BoujeeEnjinia1701/bankhaul/cad/drawings/BKH-DWG-101.pdf

### BUILD PLAN SKETCH, PLAN NOT YET BUILT BankHaul · github.com/BoujeeEnjinia1701/bankhaul

FRONT VIEW
Scale 1:20; looking at the front (along +Y)

TOP VIEW
Scale 1:20; looking down (along -Z)

RIGHT VIEW
Scale 1:20; looking at the right side (along -X)

350

500 1408

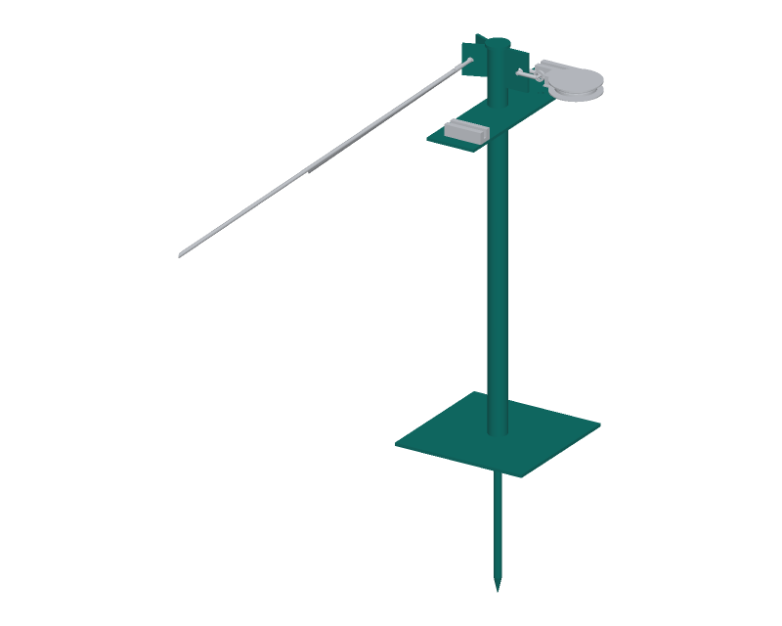
[picture p33: figure]

WHERE IT GOES
This part in colour, its neighbours in grey

HOW TO MAKE IT AND HOW IT FITS
Tube 992 long, ends square; foot plate 350 x 350 x 8 welded under it Spike 20 round, 400 below the plate centre, ground to a point
Cap disc 60 dia x 8 welded on the top of the tube
Pad eye 8 plate: 18 hole 64 from the post axis, 950 up, facing the water Two stay lugs 8 plate: 15 holes 960 up, 22 deg either side of straight back Cleat bar 130 x 500 x 8: 48.9 hole, slip on, top 850 up, weld all round Cleat bar holes: four 9 at 170 and 230 either side; one 15 tie-off hole Square the tube to the foot plate within 1 deg; weld all round
Check: pad eye hole and lug holes take a 10 mm shackle pin freely
REV | DESCRIPTION | DATE | BY
P1 | Making sketch for the prototype build plan | 2026-10-03 | AC
BANKHAUL | github.com/BoujeeEnjinia1701/bankhaul

## Bank post weldment: making sketch

DRAWING NO.
BKH-DWG-101

REV
P1

SHEET
1 of 1

SIZE

## ANSI B

SCALE
1:20

UNITS
mm
PROJECTION | DATE
2026-10-03

DRAWN
Amish Chadha

MATERIAL / NOTES
48.3 x 3.2 tube; 8 mm plate; 20 mm round bar; zinc-rich paint
Licensed CERN-OHL-S-2.0 · Design Molecule Lab · designmolecule.com | Generated from cad/src; do not edit by hand
