BoujeeEnjinia1701/bankhaul/cad/drawings/BKH-DWG-106.pdf

### BUILD PLAN SKETCH, PLAN NOT YET BUILT BankHaul · github.com/BoujeeEnjinia1701/bankhaul

FRONT VIEW
Scale 1:5; looking at the front (along +Y)

TOP VIEW
Scale 1:5; looking down (along -Z)

RIGHT VIEW
Scale 1:5; looking at the right side (along -X)

657

16 92

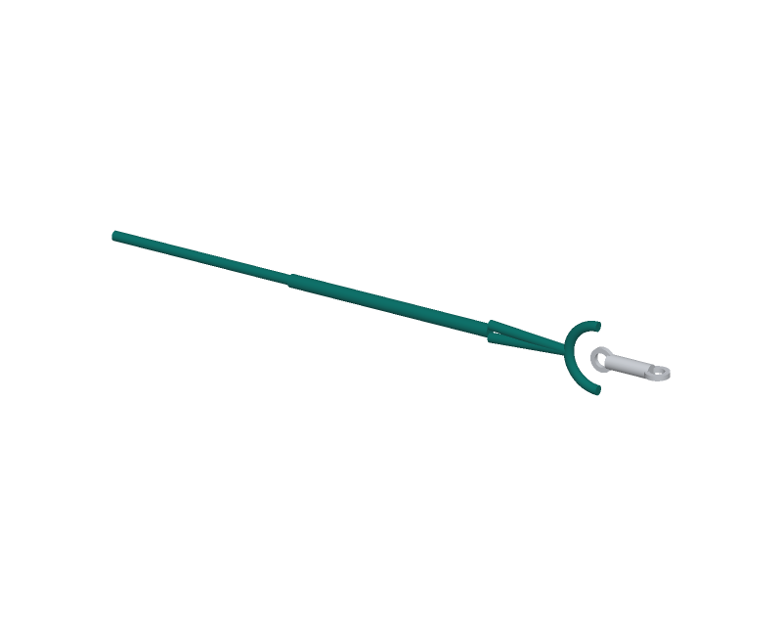
[picture p34: figure]

WHERE IT GOES
This part in colour, its neighbours in grey

HOW TO MAKE IT AND HOW IT FITS
Cut two halves of 55 m from the 120 m coil; tape and melt the ends Splice a soft eye 80 long round one swivel eye in each half; five tucks Lead each plain end round the other ring: round turn and two half hitches Set the length so the rings lie at the blocks when the loop is snug
Seize the knot's tail and coil any surplus at the ring, never between rings Check: each ring turns freely on its swivel under a hand pull
REV | DESCRIPTION | DATE | BY
P1 | Making sketch for the prototype build plan | 2026-10-03 | AC
BANKHAUL | github.com/BoujeeEnjinia1701/bankhaul

## Rope loop half and swivel ring: making sketch

DRAWING NO.
BKH-DWG-106

REV
P1

SHEET
1 of 1

SIZE

## ANSI B

SCALE
1:5

UNITS
mm
PROJECTION | DATE
2026-10-03

DRAWN
Amish Chadha

MATERIAL / NOTES
12 mm floating polysteel rope; eye-to-eye swivel
Licensed CERN-OHL-S-2.0 · Design Molecule Lab · designmolecule.com | Generated from cad/src; do not edit by hand
