BoujeeEnjinia1701/bankhaul/cad/drawings/BKH-DWG-107.pdf

### BUILD PLAN SKETCH, PLAN NOT YET BUILT BankHaul · github.com/BoujeeEnjinia1701/bankhaul

FRONT VIEW
Scale 1:20; looking at the front (along +Y)

TOP VIEW
Scale 1:20; looking down (along -Z)

RIGHT VIEW
Scale 1:20; looking at the right side (along -X)

83

8 1525

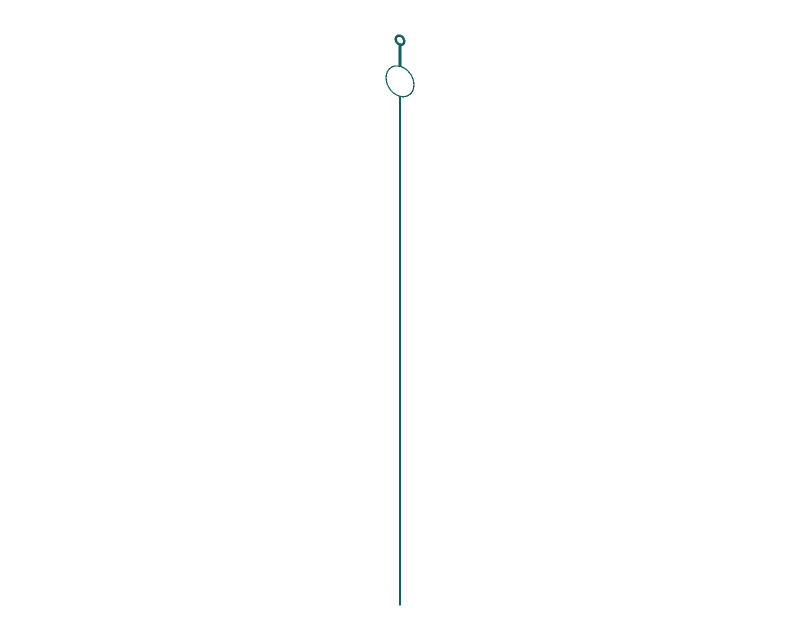
[picture p35: figure]

WHERE IT GOES
This part in colour, its neighbours in grey

HOW TO MAKE IT AND HOW IT FITS
Bridle 1,500 of 6 mm cord; bowline to the net's head and foot ropes
Weak link: one loop of the chosen cord, 80 long, joining hook and bridle Choose the cord by pulling three samples: each must release at 500 to 700 N Snap hook clips to a swivel ring (far end) or the tie-off hole (near end)
Make two; mark the weak link cord with paint so it is never swapped
Check: the hook opens with one hand and snaps shut by itself
REV | DESCRIPTION | DATE | BY
P1 | Making sketch for the prototype build plan | 2026-10-03 | AC
BANKHAUL | github.com/BoujeeEnjinia1701/bankhaul

## Net bridle with weak link: making sketch

DRAWING NO.
BKH-DWG-107

REV
P1

SHEET
1 of 1

SIZE

## ANSI B

SCALE
1:20

UNITS
mm
PROJECTION | DATE
2026-10-03

DRAWN
Amish Chadha

MATERIAL / NOTES
6 mm polyester cord; braided weak link cord; 60 mm stainless snap hook
Licensed CERN-OHL-S-2.0 · Design Molecule Lab · designmolecule.com | Generated from cad/src; do not edit by hand
