BoujeeEnjinia1701/bankhaul/cad/drawings/BKH-DWG-001.png

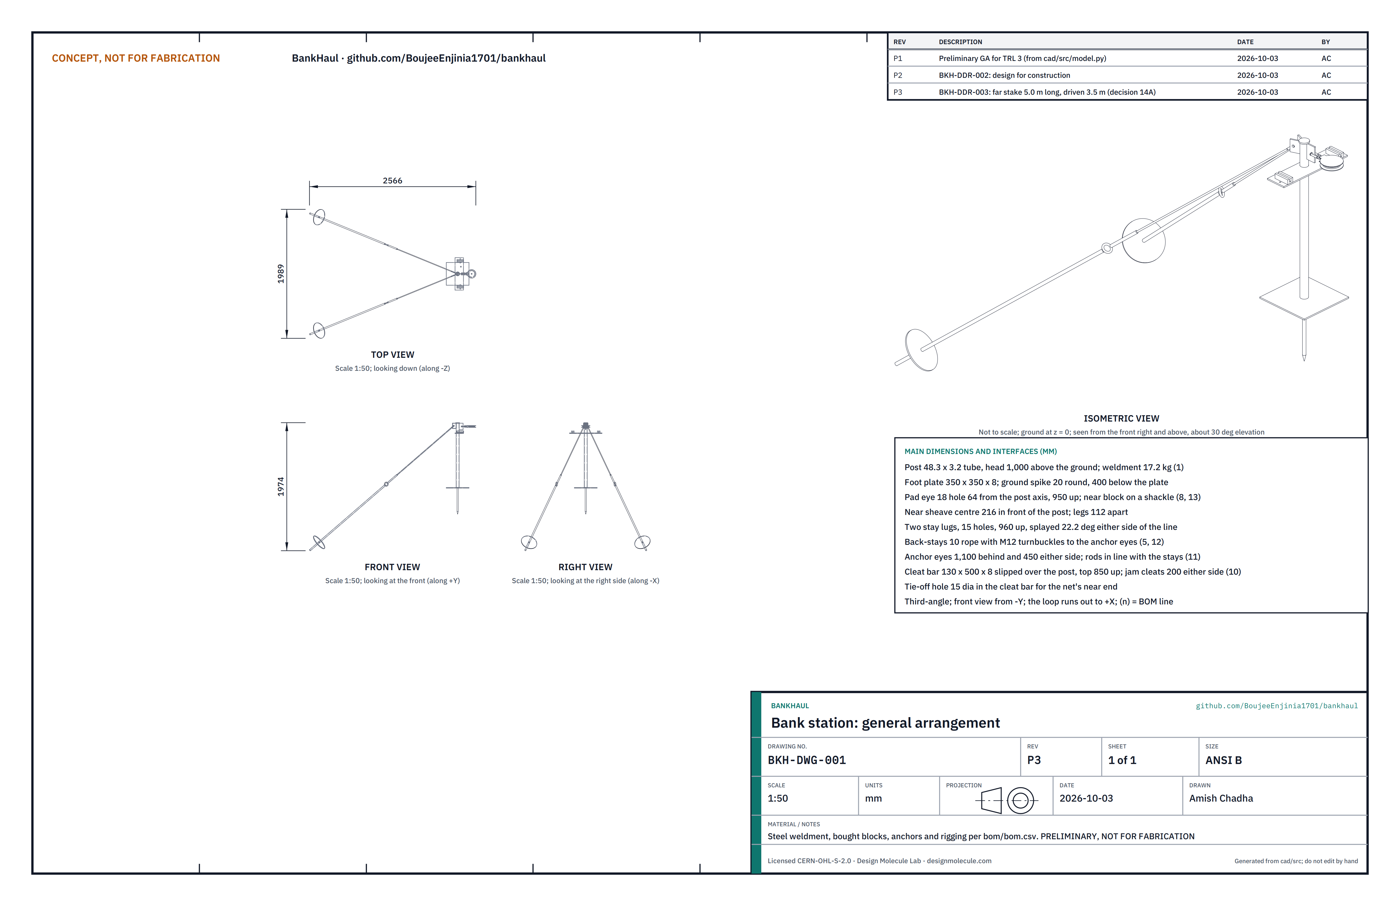
cad/drawings/BKH-DWG-001.png
