BoujeeEnjinia1701/bankhaul/cad/drawings/BKH-DWG-002.png

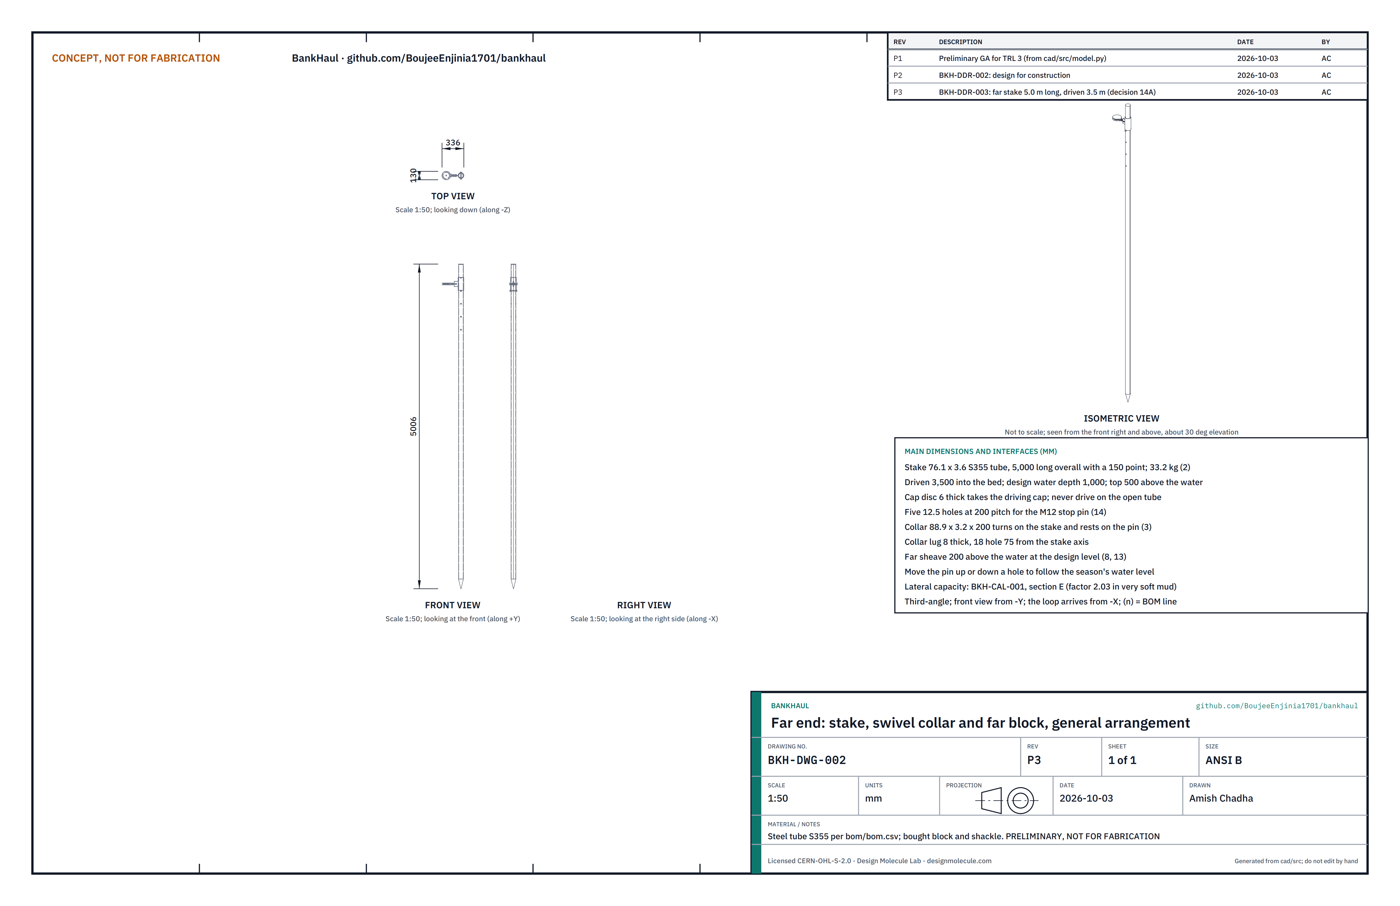
cad/drawings/BKH-DWG-002.png
