BoujeeEnjinia1701/bankhaul/cad/drawings/BKH-DWG-003.png

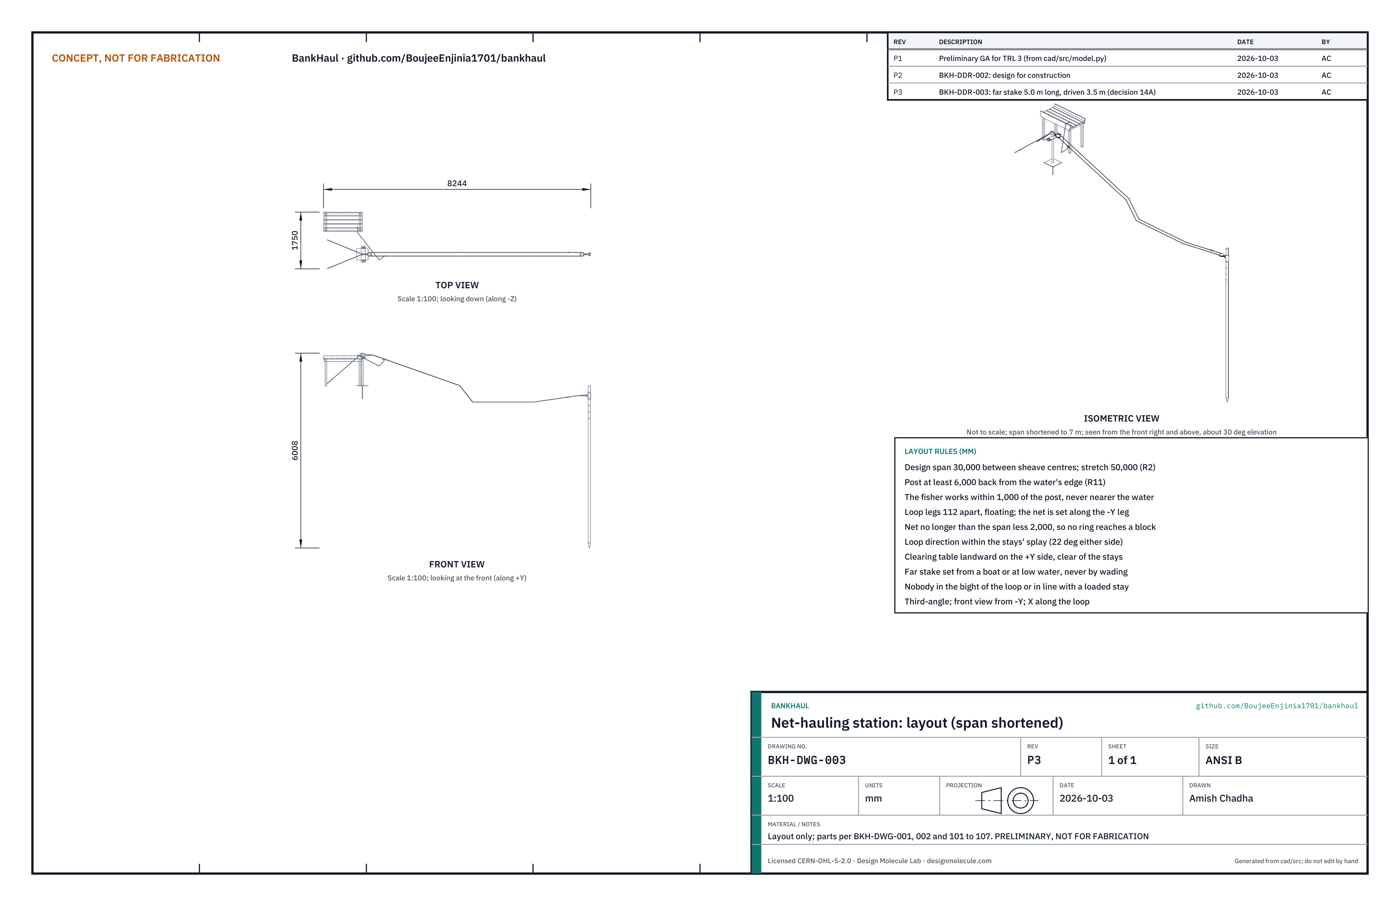
cad/drawings/BKH-DWG-003.png
