BoujeeEnjinia1701/bankhaul/media/card.png

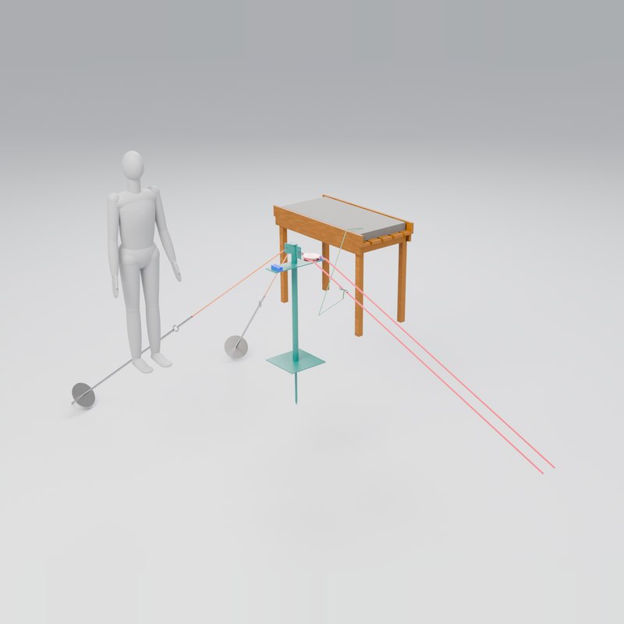
media/card.png
