BoujeeEnjinia1701/bankhaul/media/exploded.png

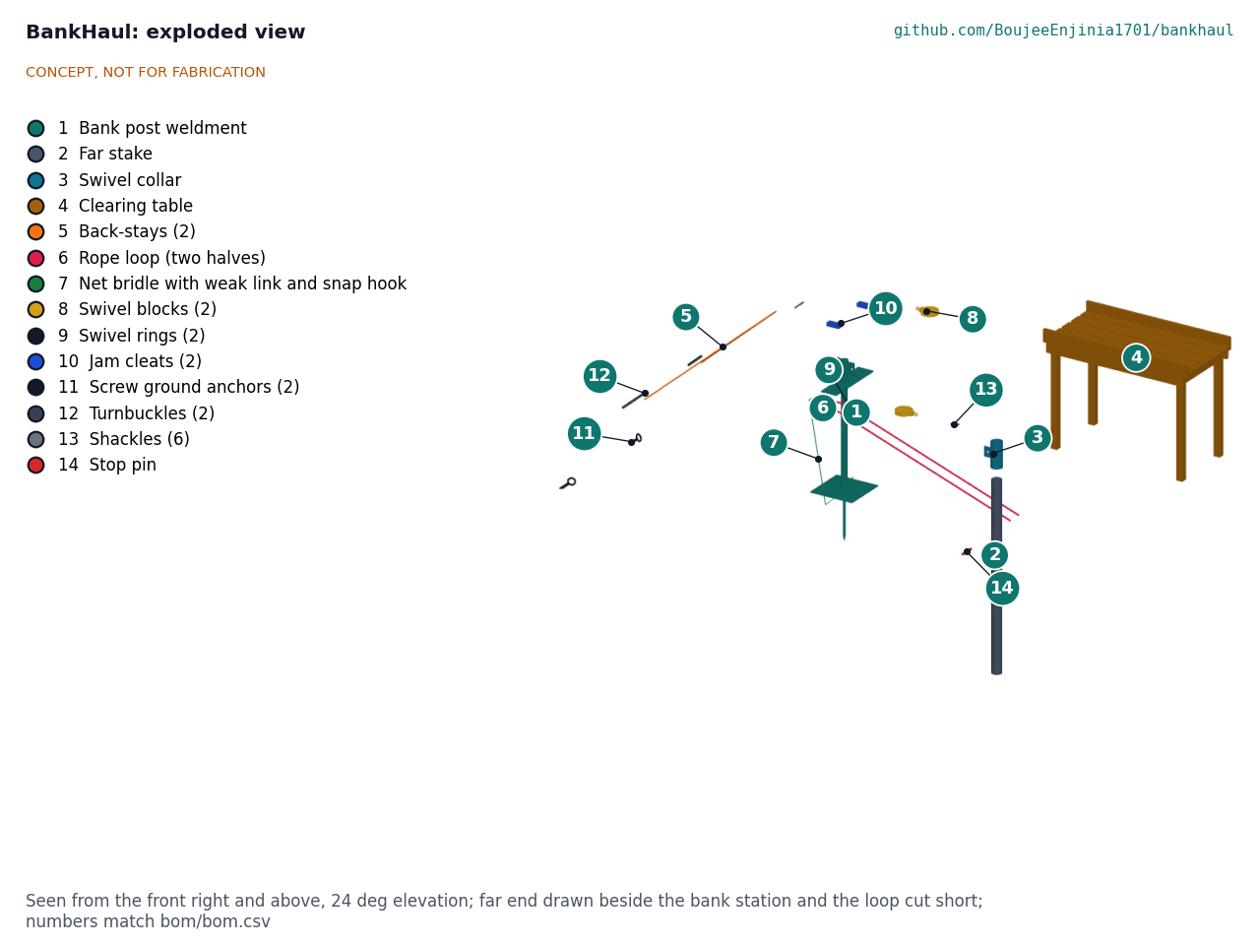
media/exploded.png
