BoujeeEnjinia1701/bankhaul/media/flow.png

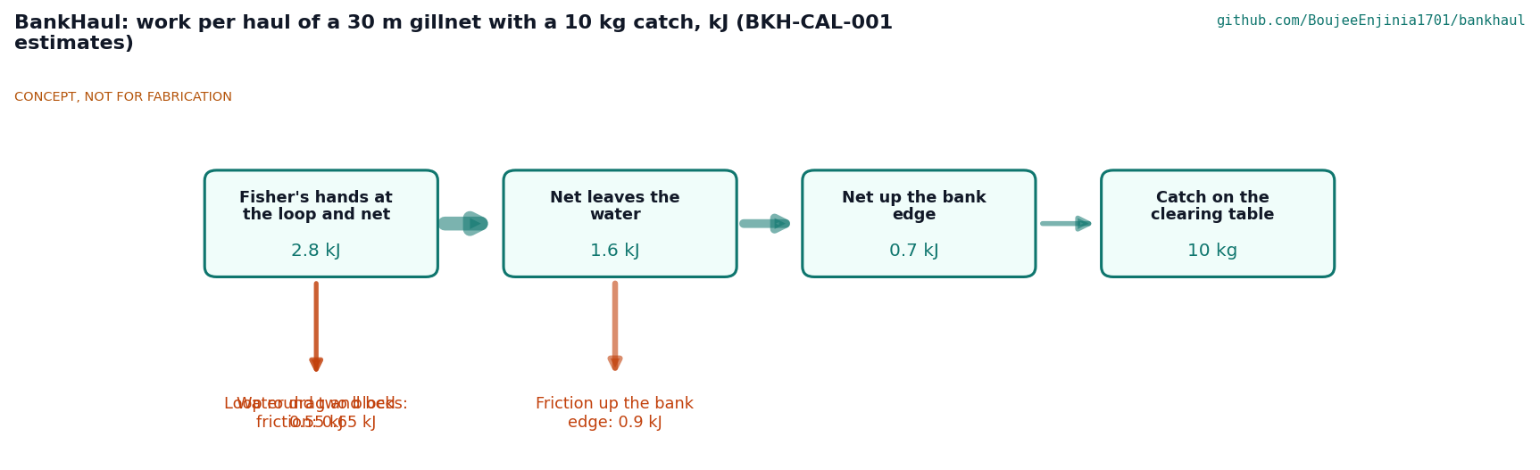
media/flow.png
