BoujeeEnjinia1701/bankhaul/media/render-detail.png

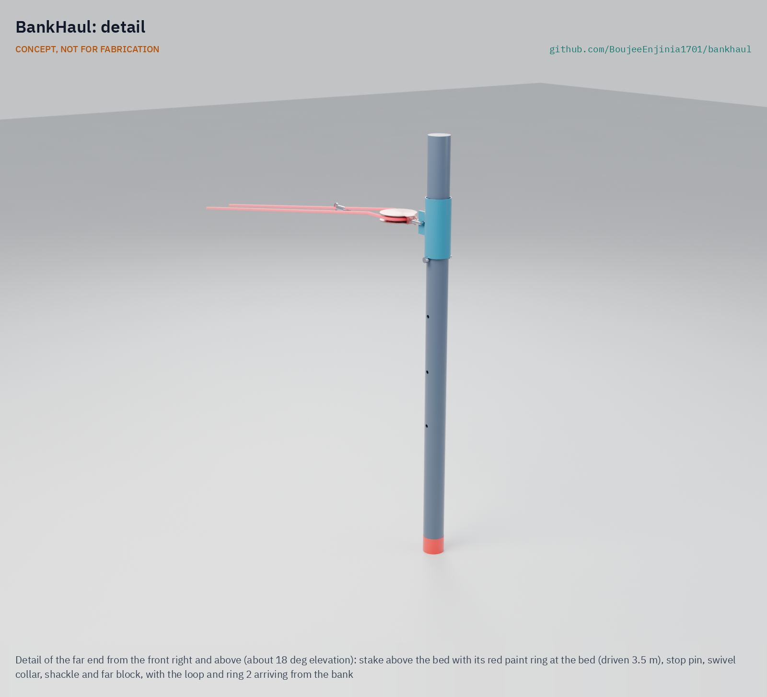
media/render-detail.png
