BoujeeEnjinia1701/bankhaul/media/render-exploded.png

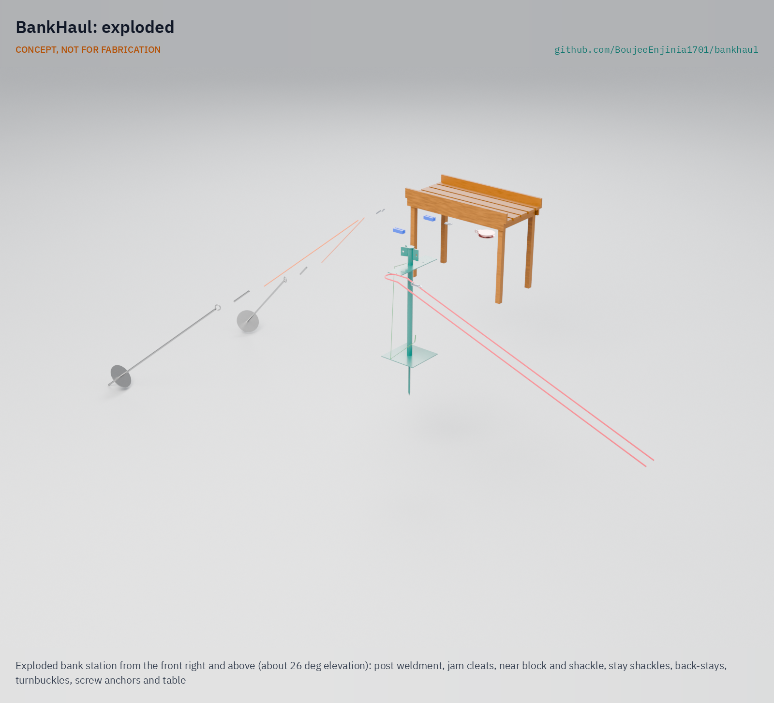
media/render-exploded.png
