BoujeeEnjinia1701/bankhaul/media/social-preview.png

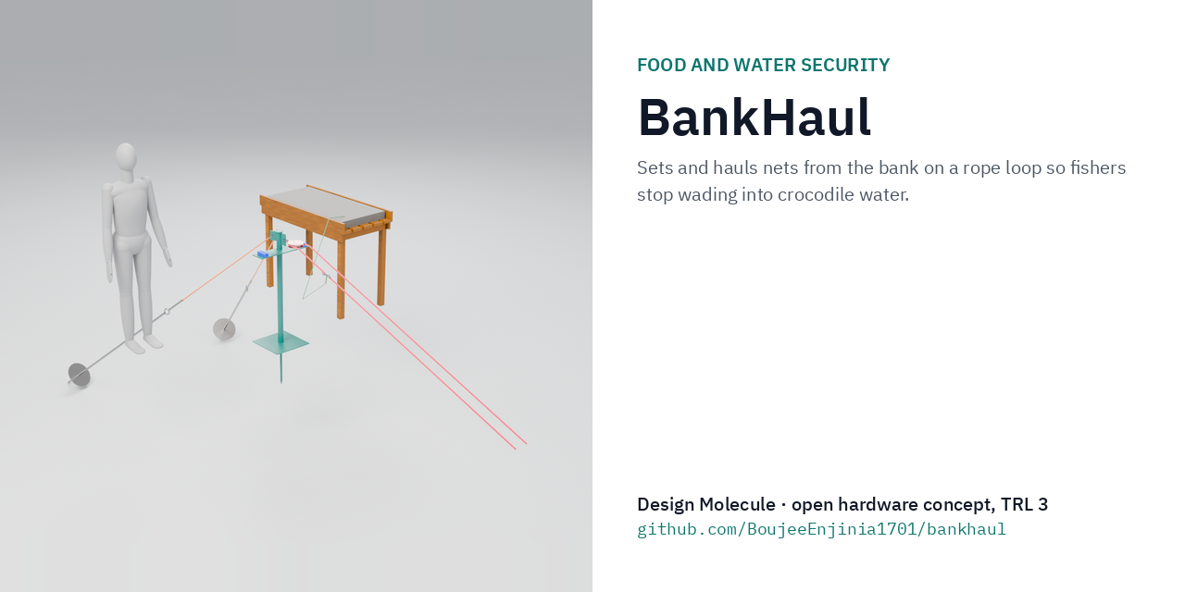
media/social-preview.png
