BoujeeEnjinia1701/bankhaul/cad/drawings/BKH-DWG-103.pdf

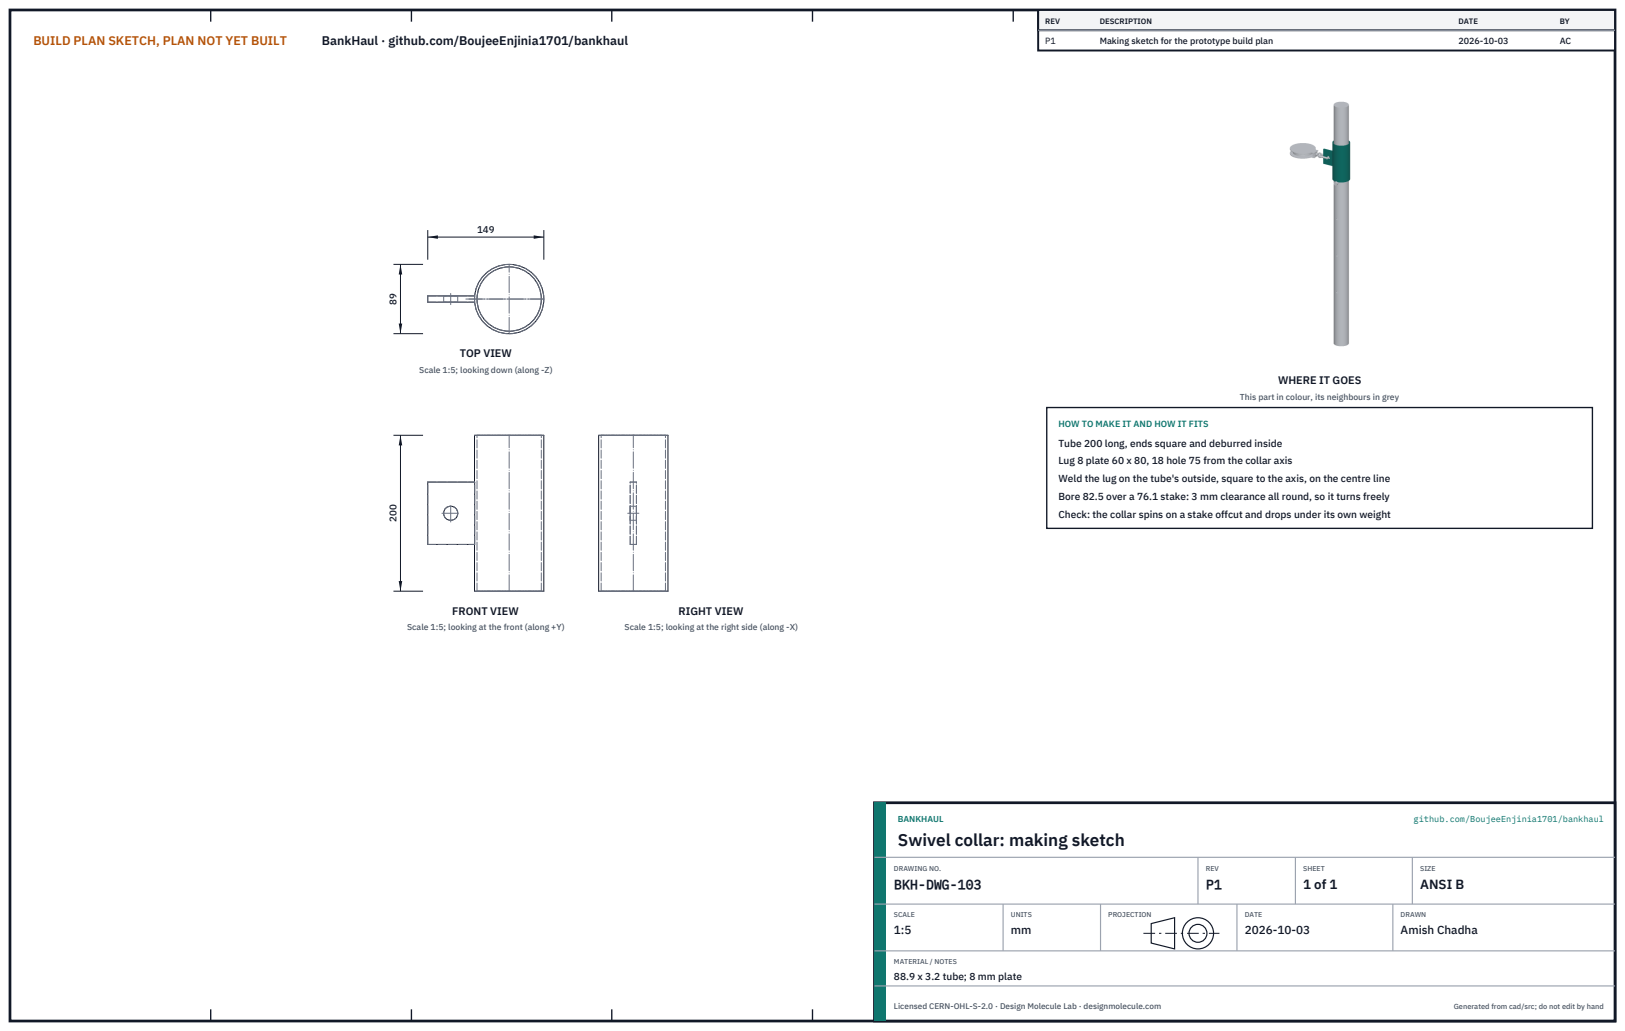
[picture p55: page 1]
BUILD PLAN SKETCH, PLAN NOT YET BUILT; BankHaul · github.com/BoujeeEnjinia1701/bankhaul; FRONT VIEW; TOP VIEW; RIGHT VIEW; REV; DESCRIPTION; DATE; Making sketch for the prototype build plan; BANKHAUL; github.com/BoujeeEnjinia1701/bankhaul; DRAWING NO. BKH-DWG-103; REV P1; SHEET 1 of 1; SIZE ANSI B; SCALE 1:5; UNITS mm; PROJECTION; DRAWN Amish Chadha; Licensed CERN-OHL-S-2.0 · Design Molecule Lab · designmolecule.com; Generated from cad/src; do not edit by hand

Scale 1:5; looking down (along -Z)

WHERE IT GOES

This part in colour, its neighbours in grey

HOW TO MAKE IT AND HOW IT FITS
Tube 200 long, ends square and deburred inside
Lug 8 plate 60 x 80, 18 hole 75 from the collar axis
Weld the lug on the tube's outside, square to the axis, on the centre line
Bore 82.5 over a 76.1 stake: 3 mm clearance all round, so it turns freely
Check: the collar spins on a stake offcut and drops under its own weight

Scale 1:5; looking at the front (along +Y)

Scale 1:5; looking at the right side (along -X)

Swivel collar: making sketch

MATERIAL / NOTES
88.9 x 3.2 tube; 8 mm plate
