BoujeeEnjinia1701/bankhaul/cad/drawings/BKH-DWG-104.pdf

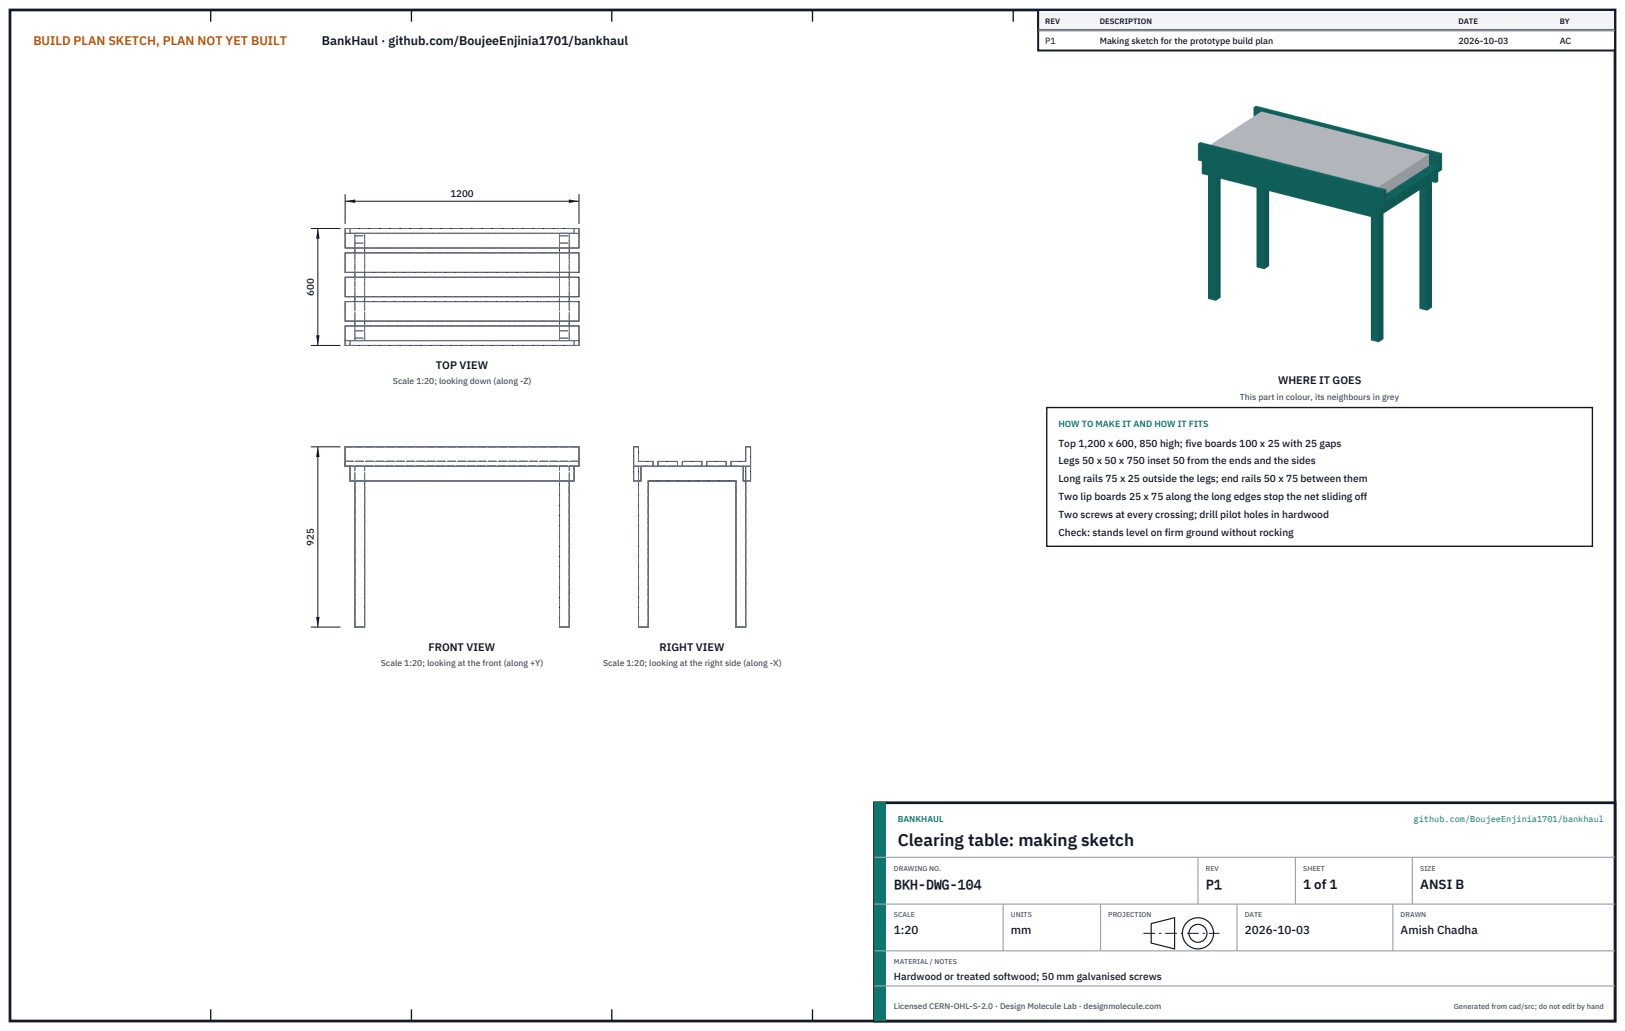
[picture p56: page 1]
BUILD PLAN SKETCH, PLAN NOT YET BUILT; BankHaul · github.com/BoujeeEnjinia1701/bankhaul; FRONT VIEW; TOP VIEW; RIGHT VIEW; REV; DESCRIPTION; DATE; Making sketch for the prototype build plan; BANKHAUL; github.com/BoujeeEnjinia1701/bankhaul; DRAWING NO. BKH-DWG-104; REV P1; SHEET 1 of 1; SIZE ANSI B; SCALE 1:20; UNITS mm; PROJECTION; DRAWN Amish Chadha; Licensed CERN-OHL-S-2.0 · Design Molecule Lab · designmolecule.com; Generated from cad/src; do not edit by hand

Scale 1:20; looking down (along -Z)

WHERE IT GOES

This part in colour, its neighbours in grey

HOW TO MAKE IT AND HOW IT FITS
Top 1,200 x 600, 850 high; five boards 100 x 25 with 25 gaps
Legs 50 x 50 x 750 inset 50 from the ends and the sides
Long rails 75 x 25 outside the legs; end rails 50 x 75 between them
Two lip boards 25 x 75 along the long edges stop the net sliding off
Two screws at every crossing; drill pilot holes in hardwood
Check: stands level on firm ground without rocking

Scale 1:20; looking at the front (along +Y)

Scale 1:20; looking at the right side (along -X)

Clearing table: making sketch

MATERIAL / NOTES
Hardwood or treated softwood; 50 mm galvanised screws
