BoujeeEnjinia1701/bankhaul/cad/drawings/BKH-DWG-105.pdf

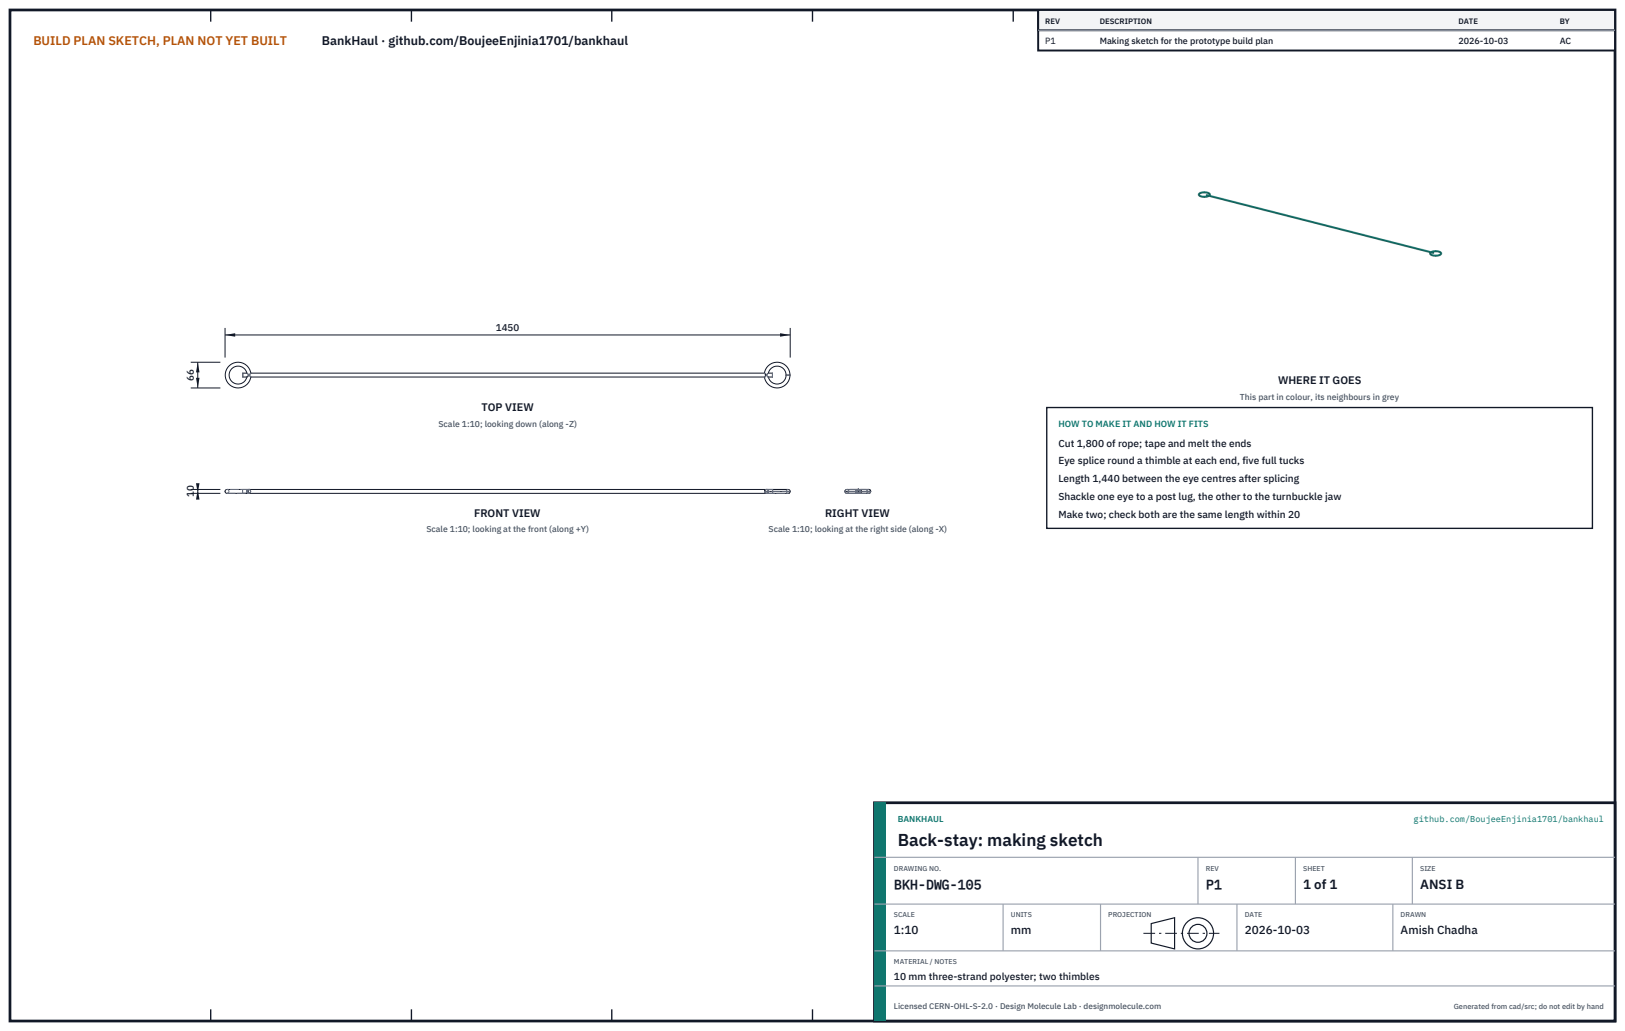
[picture p57: page 1]
BUILD PLAN SKETCH, PLAN NOT YET BUILT; BankHaul · github.com/BoujeeEnjinia1701/bankhaul; FRONT VIEW; TOP VIEW; RIGHT VIEW; REV; DESCRIPTION; DATE; Making sketch for the prototype build plan; BANKHAUL; github.com/BoujeeEnjinia1701/bankhaul; DRAWING NO. BKH-DWG-105; REV P1; SHEET 1 of 1; SIZE ANSI B; SCALE 1:10; UNITS mm; PROJECTION; DRAWN Amish Chadha; Licensed CERN-OHL-S-2.0 · Design Molecule Lab · designmolecule.com; Generated from cad/src; do not edit by hand

WHERE IT GOES

This part in colour, its neighbours in grey

Scale 1:10; looking down (along -Z)

HOW TO MAKE IT AND HOW IT FITS
Cut 1,800 of rope; tape and melt the ends
Eye splice round a thimble at each end, five full tucks
Length 1,440 between the eye centres after splicing
Shackle one eye to a post lug, the other to the turnbuckle jaw
Make two; check both are the same length within 20

Scale 1:10; looking at the front (along +Y)

Scale 1:10; looking at the right side (along -X)

Back-stay: making sketch

MATERIAL / NOTES
10 mm three-strand polyester; two thimbles
